neon99999/GRT_Orb/Arduino/src/config.cpp

// config.cpp
#include "config.h"

// pick profile heree
enum Profile
{
  Studio,
  Theatre
};
static Profile ACTIVE_PROFILE = Theatre;

// Declarations
const char *WIFI_SSID;
const char *WIFI_PASSWORD;

uint16_t E131_UNIVERSE;
uint16_t START_ADDR;
bool USE_UNICAST;

int NUM_PIXELS;

uint8_t DEFAULT_BRIGHTNESS_CAP;
uint32_t DMX_TIMEOUT_MS;

bool USE_STATIC_IP;
IPAddress STATIC_IP, STATIC_GW, STATIC_SN, STATIC_DNS;

uint8_t RUN_MODE = MODE_PERPIXEL;

// ---------- Loaders ----------
static void loadStudio()
{
  WIFI_SSID = "CuatroCabezas";
  WIFI_PASSWORD = "xxxx";

  E131_UNIVERSE = 1;
  START_ADDR = 321;
  USE_UNICAST = true;

  // NUM_PIXELS is the count you can control from DMX.
  // Physical strip will be treated as NUM_PIXELS + 1 (pixel 0 reserved).
  NUM_PIXELS = 23;
  DEFAULT_BRIGHTNESS_CAP = 200;

  DMX_TIMEOUT_MS = 3000;

  RUN_MODE = MODE_PERPIXEL;

  USE_STATIC_IP = true;
  STATIC_IP = IPAddress(192, 168, 1, 99);
  STATIC_GW = IPAddress(192, 168, 1, 1);
  STATIC_SN = IPAddress(255, 255, 255, 0);
  STATIC_DNS = IPAddress(192, 168, 1, 1);
}

static void loadTheatre()
{
  WIFI_SSID = "ORB";
  WIFI_PASSWORD = "orbAdmin2025";

  E131_UNIVERSE = 1;
  START_ADDR = 321;
  USE_UNICAST = true;

  // NUM_PIXELS is the count you can control from DMX.
  // Physical strip will be treated as NUM_PIXELS + 1 (pixel 0 reserved).
  NUM_PIXELS = 23;
  DEFAULT_BRIGHTNESS_CAP = 200;

  DMX_TIMEOUT_MS = 3000;

  RUN_MODE = MODE_PERPIXEL;

  USE_STATIC_IP = true;
  STATIC_IP = IPAddress(10, 10, 50, 201);
  STATIC_GW = IPAddress(10, 10, 50, 1);
  STATIC_SN = IPAddress(255, 255, 255, 0);
  STATIC_DNS = IPAddress(10, 10, 50, 1);
}

// Auto-load
__attribute__((constructor)) static void loadProfile()
{
  if (ACTIVE_PROFILE == Theatre)
    loadTheatre();
  else
    loadStudio();
}
